MKonovalov/PLFM_RADAR/4_Schematics and Boards Layout/4_7_Production Files/Board_Artifacts/PowerBoard_bom.csv

Designator | Value | Device | Deviceset | Package | Library | PartNo | DNP
C1 | 0.1µF |  |  | C0805 | rcl
C10 | 10µF |  |  | C0805 | rcl
C100 | T521W476M020ATE045 |  |  | T521W | T521W476M020ATE045
C101 | T521W476M020ATE045 |  |  | T521W | T521W476M020ATE045
C102 | T521W476M020ATE045 |  |  | T521W | T521W476M020ATE045
C103 | T521W476M020ATE045 |  |  | T521W | T521W476M020ATE045
C104 | T521W476M020ATE045 |  |  | T521W | T521W476M020ATE045
C105 | T521W476M020ATE045 |  |  | T521W | T521W476M020ATE045
C106 | 1µF |  |  | C0805 | rcl
C107 | 1µF |  |  | C0805 | rcl
C108 | 10µF |  |  | C0805 | rcl
C109 | 0.1µF |  |  | C0805 | rcl
C11 | 22µF |  |  | C0603 | rcl
C110 | 22µF |  |  | C0603 | rcl
C111 | 22µF |  |  | C0603 | rcl
C112 | 10µF |  |  | C0805 | rcl
C113 | 10µF |  |  | C0805 | rcl
C114 | 10µF |  |  | C0805 | rcl
C115 | 10µF |  |  | C0805 | rcl
C116 | 1µF |  |  | C0805 | rcl
C117 | 1µF |  |  | C0805 | rcl
C118 | 10µF |  |  | C0805 | rcl
C119 | 0.1µF |  |  | C0805 | rcl
C12 | 0.1µF |  |  | C0805 | rcl
C120 | 22µF |  |  | C0603 | rcl
C121 | 22µF |  |  | C0603 | rcl
C122 | 10µF |  |  | C0805 | rcl
C123 | 10µF |  |  | C0805 | rcl
C124 | 10µF |  |  | C0805 | rcl
C125 | 10µF |  |  | C0805 | rcl
C126 | 1µF |  |  | C0805 | rcl
C127 | 1µF |  |  | C0805 | rcl
C128 | 10µF |  |  | C0805 | rcl
C129 | 0.1µF |  |  | C0805 | rcl
C13 | 22µF |  |  | C0603 | rcl
C130 | 22µF |  |  | C0603 | rcl
C131 | 22µF |  |  | C0603 | rcl
C132 | 10µF |  |  | C0805 | rcl
C133 | 10µF |  |  | C0805 | rcl
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
X40 | 22-23-2021 |  |  | 22-23-2021 | con-molex
X5 | 22-23-2021 |  |  | 22-23-2021 | con-molex
X6 | 22-23-2021 |  |  | 22-23-2021 | con-molex
X7 | 22-23-2021 |  |  | 22-23-2021 | con-molex
X8 | 22-23-2021 |  |  | 22-23-2021 | con-molex
X9 | 22-23-2021 |  |  | 22-23-2021 | con-molex
