MKonovalov/PLFM_RADAR/4_Schematics and Boards Layout/4_7_Production Files/Board_Artifacts/FreqSynth_bom.csv

Designator | Value | Device | Deviceset | Package | Library | PartNo | DNP
C1 | 10pF |  |  | C0201 | rcl
C10 | 0.47µF |  |  | C0201 | rcl
C11 | 1µF |  |  | C0201 | rcl
C12 | 1µF |  |  | C0201 | rcl
C13 | 1µF |  |  | C0201 | rcl
C14 | 1µF |  |  | C0201 | rcl
C15 | 10nF |  |  | C0402 | rcl
C16 | 0.1µF |  |  | C0201 | rcl
C17 | 10nF |  |  | C0402 | rcl
C18 | 0.1µF |  |  | C0201 | rcl
C19 | 10nF |  |  | C0402 | rcl
C2 | 0.33µF |  |  | C0201 | rcl
C20 | 0.1µF |  |  | C0201 | rcl
C21 | 22µF |  |  | C1210 | rcl
C22 | 0.1µF |  |  | C0201 | rcl
C23 | 10µF |  |  | C1210 | rcl
C24 | 0.1µF |  |  | C0201 | rcl
C25 | 22µF |  |  | C1210 | rcl
C26 | 0.1µF |  |  | C0201 | rcl
C27 | 10µF |  |  | C1210 | rcl
C28 | 0.1µF |  |  | C0201 | rcl
C29 | 22µF |  |  | C1210 | rcl
C3 | 0.47µf |  |  | C0201 | rcl
C30 | 0.1µF |  |  | C0201 | rcl
C31 | 10µF |  |  | C1210 | rcl
C32 | 0.1µF |  |  | C0201 | rcl
C33 | 22µF |  |  | C1210 | rcl
C34 | 0.1µF |  |  | C0201 | rcl
C35 | 0.1µF |  |  | C0201 | rcl
C36 | 0.1µF |  |  | C0201 | rcl
C37 | 0.1µF |  |  | C0201 | rcl
C38 | 4.7µF |  |  | C0201 | rcl
C39 | 4.7µF |  |  | C0201 | rcl
C4 |  |  |  | C0201 | rcl
C40 | 4.7µF |  |  | C0201 | rcl
C41 | 0.1µF |  |  | C0201 | rcl
C42 | 0.1µF |  |  | C0201 | rcl
C43 | 0.1µF |  |  | C0201 | rcl
C44 | 0.1µF |  |  | C0201 | rcl
C45 | 10µF |  |  | C1210 | rcl
C46 | 22µF |  |  | C1210 | rcl
C47 | 10µF |  |  | C1210 | rcl
C48 | 4.7µF |  |  | C0201 | rcl
C49 | 4.7µF |  |  | C0201 | rcl
C5 |  |  |  | C0201 | rcl
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
R8 | 0.65k |  |  | R0201 | rcl
R9 | 1k |  |  | R0201 | rcl
U1 | ADF4382ABCCZ |  |  | CC-48-10_ADI | My_Library_RADAR
U10 | ATS1005-3DB-FD-T05 |  |  | SMT_DB-FD-T05_SUS | My_Library_RADAR
U2 | MTX2-143+ |  |  | DQ1225_MNC | My_Library_RADAR
U3 | MTX2-143+ |  |  | DQ1225_MNC | My_Library_RADAR
U4 | ATS1005-3DB-FD-T05 |  |  | SMT_DB-FD-T05_SUS | My_Library_RADAR
U5 | ATS1005-3DB-FD-T05 |  |  | SMT_DB-FD-T05_SUS | My_Library_RADAR
U6 | ADF4382ABCCZ |  |  | CC-48-10_ADI | My_Library_RADAR
U7 | MTX2-143+ |  |  | DQ1225_MNC | My_Library_RADAR
U8 | ATS1005-3DB-FD-T05 |  |  | SMT_DB-FD-T05_SUS | My_Library_RADAR
U9 | MTX2-143+ |  |  | DQ1225_MNC | My_Library_RADAR
X10 | 22-23-2021 |  |  | 22-23-2021 | con-molex
X11 | 22-23-2021 |  |  | 22-23-2021 | con-molex
X12 | 22-23-2021 |  |  | 22-23-2021 | con-molex
X13 | 22-23-2021 |  |  | 22-23-2021 | con-molex
X14 | 22-23-2021 |  |  | 22-23-2021 | con-molex
X15 | 22-23-2021 |  |  | 22-23-2021 | con-molex
X4 | ECOC-2522-100.000-3HC |  |  | SMD5_ECOC-2522_25P4X22_ECS | My_Library_RADAR
X5 | CVHD-950-50.000 |  |  | SMD4_CVHD-950_CRX | My_Library_RADAR
X6 | CVHD-950-50.000 |  |  | SMD4_CVHD-950_CRX | My_Library_RADAR
