MKonovalov/PLFM_RADAR/9_Firmware/9_1_Microcontroller/9_1_1_C_Cpp_Libraries/AD9484_SPI.h

/**
 * @file    AD9484_SPI.h
 * @brief   The AD9484's serial port, which until now could not be used at all (issue #14).
 *
 * The part's CSB was tied to a supply rail - the datasheet names that as the way to disable the
 * SPI - SCLK/DFS was decided by solder jumper SJ1, and SDIO was not connected. The pins are
 * DRVDD-referenced 1.8 V logic (absolute maximum "SDIO/DCS to DRGND: -0.3 V to DRVDD + 0.2 V",
 * i.e. 2.0 V), so they now reach the MCU through a TXS0104E translator rather than being driven
 * from a 3.3 V bank.
 *
 * The master is the MCU: the ADC, the FPGA and the MCU are all on the main board, the MCU owns
 * bring-up, and the port is slow (tCLK >= 40 ns, 25 MHz maximum), so bit-banging is ample.
 *
 * Frame, from the datasheet's serial timing (and AN-877, which the datasheet points at):
 * a 16-bit instruction - R/W, W1, W0, A12..A0 - followed by 8 bits of data, MSB first. CSB
 * falling starts the frame. Readback turns SDIO around after the instruction, which is why the
 * I/O hook takes a direction control.
 *
 * The registers used here are the ones the AD9484 memory map names:
 *   0x0D TEST_IO      test data on the output pins in place of normal data
 *   0x14 OUTPUT_MODE  data format select: 00 = offset binary (default), 01 = twos complement
 *   0x19/0x1A         user pattern 1, LSB/MSB
 *   0x1B/0x1C         user pattern 2, LSB/MSB
 *   0x2A OVR_CONFIG   OR+/- enable, default on
 */
#ifndef AD9484_SPI_H
#define AD9484_SPI_H

#include <stdbool.h>
#include <stddef.h>
#include <stdint.h>

/** Register addresses, from the AD9484 memory map. */
#define AD9484_REG_SPI_CONFIG   0x00u
#define AD9484_REG_DEVICE_INDEX 0x05u
#define AD9484_REG_TEST_IO      0x0Du
#define AD9484_REG_AIN_CONFIG   0x0Fu
#define AD9484_REG_OUTPUT_MODE  0x14u
#define AD9484_REG_USER_PATT1_LSB 0x19u
#define AD9484_REG_USER_PATT1_MSB 0x1Au
#define AD9484_REG_OVR_CONFIG   0x2Au
#define AD9484_REG_CHIP_GRADE   0x02u   /* read-only: speed grade and chip ID */
#define AD9484_REG_OFFSET       0x10u   /* 8-bit device offset trim, in output codes */
#define AD9484_REG_FLEX_VREF    0x18u   /* bits[7:6] VREF select, bits[4:0] input range */
#define AD9484_REG_OUTPUT_ADJUST 0x15u  /* LVDS drive strength, if the eye needs adjusting */
#define AD9484_REG_INPUT_COUPLING 0x2Cu /* default is ac coupling */
#define AD9484_VREF_SELECT_INTERNAL 0x00u  /* bits[7:6]: internal reference, 20 k pull-down */
#define AD9484_REG_DEVICE_UPDATE 0xFFu  /* writing bit 0 transfers the shift register */

/** OUTPUT_MODE data-format field: the FPGA treats the capture as unsigned, i.e. offset binary. */
#define AD9484_FORMAT_OFFSET_BINARY 0x00u
#define AD9484_FORMAT_TWOS_COMPLEMENT 0x01u

/** TEST_IO: write 0 to return the outputs to normal data. */
/*
 * The output test modes, from the datasheet's memory map (register 0x0D TEST_IO, bits[3:0]).
 *
 * There is no ramp mode.  The deterministic ones are PN9 and PN23: pseudo-random sequences with
 * defined polynomials, so a capture can be checked against a computed expectation rather than only
 * against "not constant" - which is what the acceptance means by wanting a deterministic pattern.
 * Note that the format of the pattern on the pins is set by OUTPUT_MODE, as the datasheet says.
 */
#define AD9484_TEST_OFF          0x00u   /* 0000: normal data */
#define AD9484_TEST_MIDSCALE     0x01u   /* 0001: midscale short  */
#define AD9484_TEST_POS_FS       0x02u   /* 0010: +FS short       */
#define AD9484_TEST_NEG_FS       0x03u   /* 0011: -FS short       */
#define AD9484_TEST_CHECKERBOARD 0x04u   /* 0100: checker board   */
#define AD9484_TEST_PN23         0x05u   /* 0101: PN23 sequence   */
#define AD9484_TEST_PN9          0x06u   /* 0110: PN9 sequence    */
#define AD9484_TEST_ONE_ZERO     0x07u   /* 0111: one/zero word toggle */
#define AD9484_TEST_USER_PATTERN 0x08u   /* 1000: user-defined, from 0x19/0x1A */

/** The three lines plus the turnaround control. All optional except csb/sclk/sdio_out. */
typedef struct {
    void (*csb)(bool level);
    void (*sclk)(bool level);
    void (*sdio_out)(bool level);
    void (*sdio_dir)(bool output);       /* true = drive, false = release for readback */
    bool (*sdio_in)(void);
    void (*delay_half_bit)(void);        /* >= 20 ns so tCLK >= 40 ns */
} AD9484_SPI_IO_t;

/** Bind the hooks. Returns false if the essential ones are missing. */
bool AD9484_SPI_Init(const AD9484_SPI_IO_t *io);

/** Write one 8-bit register. */
bool AD9484_SPI_WriteRegister(const AD9484_SPI_IO_t *io, uint8_t addr, uint8_t value);

/** Read one 8-bit register (SDIO turns around after the instruction). */
bool AD9484_SPI_ReadRegister(const AD9484_SPI_IO_t *io, uint8_t addr, uint8_t *value);

/**
 * Transfer the master shift register to the slave.
 *
 * This is not optional: DEVICE_UPDATE (0xFF) is what makes a write take effect.  Without it the
 * data sits in the shift register and the part never changes - which is how the test-pattern and
 * data-format helpers could report success and do nothing.
 */
bool AD9484_SPI_Commit(const AD9484_SPI_IO_t *io);

/** Device offset trim, in output codes (-128..+127).  Zero is the default. */
bool AD9484_SPI_SetOffsetTrim(const AD9484_SPI_IO_t *io, int codes);

/*
 * Set the input voltage range - which is this part's gain trim.
 *
 * The AD9484 has no register named "gain".  Its full scale is set by the input voltage range in
 * FLEX_VREF (0x18 bits[4:0]), and its zero by the offset trim above; those two are the pair the
 * datasheet means when it lists "gain adjust" among the serial-port functions.  Gain error is
 * +/-1.0% FS at 25 C, which is what trimming this removes.
 *
 * The range code is not a linear field: the map is a table in the datasheet, running from 1.20 V p-p
 * at code 0b01011 up to 1.60 V at 0b11100, with 1.50 V - the design's value and the reset default -
 * at 0b00000.  Pass the code, and use AD9484_SPI_InputRangeMillivolts() to read what it means.
 */
bool AD9484_SPI_SetInputRange(const AD9484_SPI_IO_t *io, uint8_t code);

/* The documented range for a code, in millivolts peak-to-peak, or 0 if the code is undocumented. */
int AD9484_SPI_InputRangeMillivolts(uint8_t code);

/** Read the read-only CHIP_GRADE register: a real readback from a part that answers. */
bool AD9484_SPI_ReadChipGrade(const AD9484_SPI_IO_t *io, uint8_t *grade);

/**
 * Put a user-defined pattern on the output pins, or take it off again.
 * With `on` true, `pattern` is loaded into USER_PATT1 (LSB then MSB) and TEST_IO is enabled;
 * with `on` false, TEST_IO is cleared and normal data returns.
 */
bool AD9484_SPI_SetTestPattern(const AD9484_SPI_IO_t *io, bool on, uint16_t pattern);

/*
 * Select one of the documented output test modes (the AD9484_TEST_* values above).
 * Returns false for a mode the datasheet does not document - the codes 1001 to 1111 are unused, and
 * writing them would put an unverified value in the register.
 *
 * AD9484_TEST_USER_PATTERN only selects the mode; the pattern itself is written by
 * AD9484_SPI_SetTestPattern().
 */
bool AD9484_SPI_SetTestMode(const AD9484_SPI_IO_t *io, uint8_t mode);

/* True if the mode is one the datasheet documents. */
bool AD9484_SPI_TestModeIsValid(uint8_t mode);

/** Select the output data format explicitly rather than relying on the SCLK/DFS strap. */
bool AD9484_SPI_SetDataFormat(const AD9484_SPI_IO_t *io, uint8_t format);

/**
 * Read back two registers whose defaults the datasheet states, and report whether both match.
 * This is the bring-up answer to "does the ADC respond": 0x00 CHIP_PORT_CONFIG defaults to 0x18
 * and 0x2A OVR_CONFIG to 0x01, so a mismatch - or a bus that reads all-zero or all-one - is
 * visible as a number rather than as a missing feature.  Nothing is written, so the test is
 * safe to run at any time, including on a part already configured.
 */
bool AD9484_SPI_SelfTest(const AD9484_SPI_IO_t *io, uint8_t *config_read, uint8_t *ovr_read);

#endif /* AD9484_SPI_H */
