MKonovalov/PLFM_RADAR/9_Firmware/9_1_Microcontroller/9_1_1_C_Cpp_Libraries/STROBE_ACK.c

/**
 * @file    STROBE_ACK.c
 * @brief   MCU side of the strobe acknowledgement.  See STROBE_ACK.h.
 */
#include "STROBE_ACK.h"

void StrobeAck_Init(StrobeAck_State_t *st)
{
    if (st == NULL) {
        return;
    }
    st->ack = false;
    st->sent = 0;
    st->acknowledged = 0;
    st->missed = 0;
}

void StrobeAck_BeforeSend(StrobeAck_State_t *st)
{
    if (st == NULL) {
        return;
    }
    /* Score the request that is about to be superseded.  A request that was never
     * acknowledged is a dropped strobe, and this is the last moment it can be seen: the
     * FPGA clears the line as soon as the new request arrives. */
    if (st->sent > 0 && !st->ack) {
        st->missed++;
    }
    st->sent++;
}

void StrobeAck_Sample(StrobeAck_State_t *st, bool ack)
{
    if (st == NULL) {
        return;
    }
    if (ack && !st->ack) {
        st->acknowledged++;
    }
    st->ack = ack;
}

bool StrobeAck_HasMissed(const StrobeAck_State_t *st)
{
    return st != NULL && st->missed != 0;
}

void StrobeAck_SelfTest_Begin(StrobeAck_SelfTest_t *t, uint32_t timeout_ms)
{
    if (t == NULL) {
        return;
    }
    t->timeout_ms = timeout_ms;
    t->waited_ms = 0;
    t->running = true;
    t->passed = false;
}

StrobeAck_SelfTestResult_t StrobeAck_SelfTest_Poll(StrobeAck_SelfTest_t *t, uint32_t elapsed_ms,
                                                   bool ack)
{
    if (t == NULL || !t->running) {
        return STROBE_SELFTEST_TIMEOUT;
    }
    if (ack) {
        t->running = false;
        t->passed = true;
        return STROBE_SELFTEST_PASSED;
    }
    t->waited_ms += elapsed_ms;
    if (t->waited_ms >= t->timeout_ms) {
        t->running = false;
        return STROBE_SELFTEST_TIMEOUT;
    }
    return STROBE_SELFTEST_WAITING;
}
