MKonovalov/PLFM_RADAR/9_Firmware/9_1_Microcontroller/tests/test_agc_outer_loop.cpp

// test_agc_outer_loop.cpp -- C++ unit tests for ADAR1000_AGC outer-loop AGC
//
// Tests the STM32 outer-loop AGC class that adjusts ADAR1000 VGA gain based
// on the FPGA's saturation flag.  Uses the existing HAL mock/spy framework.
//
// Build: c++ -std=c++17 ... (see Makefile TESTS_WITH_CXX rule)

#include <cassert>
#include <cstdio>
#include <cstring>

// Shim headers override real STM32/diag headers
#include "stm32_hal_mock.h"
#include "ADAR1000_AGC.h"
#include "AgcPulseCounter.h"
#include "ADAR1000_Manager.h"

// ---------------------------------------------------------------------------
// Linker symbols required by ADAR1000_Manager.cpp (pulled in via main.h shim)
// ---------------------------------------------------------------------------
uint8_t GUI_start_flag_received = 0;
uint8_t USB_Buffer[64] = {0};
extern "C" void Error_Handler(void) {}

// ---------------------------------------------------------------------------
// Helpers
// ---------------------------------------------------------------------------

static int tests_passed = 0;
static int tests_total  = 0;

#define RUN_TEST(fn)                                                           \
    do {                                                                        \
        tests_total++;                                                          \
        printf("  [%2d] %-55s ", tests_total, #fn);                            \
        fn();                                                                   \
        tests_passed++;                                                         \
        printf("PASS\n");                                                       \
    } while (0)

// ---------------------------------------------------------------------------
// Test 1: Default construction matches design spec
// ---------------------------------------------------------------------------
static void test_defaults()
{
    ADAR1000_AGC agc;

    assert(agc.agc_base_gain == 30);  // kDefaultRxVgaGain
    assert(agc.gain_step_down == 4);
    assert(agc.gain_step_up == 2);   // Phase 1: was 1 -> ~31 s blind window
    assert(agc.min_gain == 0);
    assert(agc.max_gain == 127);
    assert(agc.holdoff_frames == 1); // Phase 1: was 4
    assert(agc.enabled == false);  // disabled by default — FPGA DIG_6 is source of truth
    assert(agc.holdoff_counter == 0);
    assert(agc.last_saturated == false);
    assert(agc.saturation_event_count == 0);

    // All cal offsets zero
    for (int i = 0; i < AGC_TOTAL_CHANNELS; ++i) {
        assert(agc.cal_offset[i] == 0);
    }
}
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
